jbilander/Amiga_Mean_Well_RT-50B_PSU_Mount/images/V2/Amiga_Mean_Well_RT-50B_PSU_Mount_V2_pic47.jpg

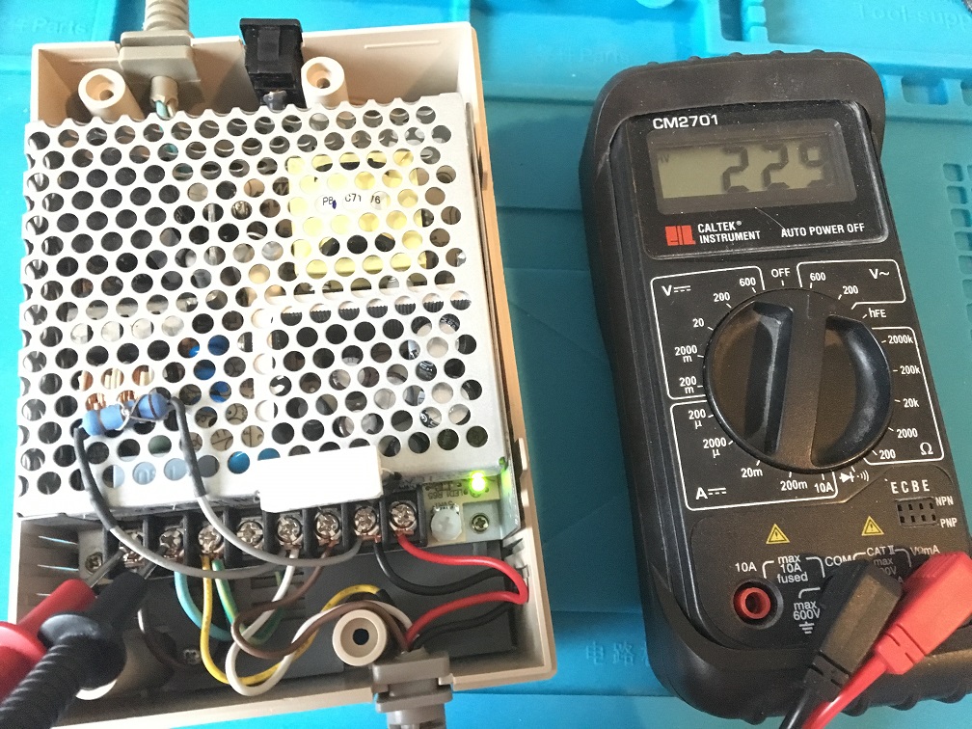
images/V2/Amiga_Mean_Well_RT-50B_PSU_Mount_V2_pic47.jpg
